BogdanVcode/fotobudka-dashboard/assets/references/04-module.png

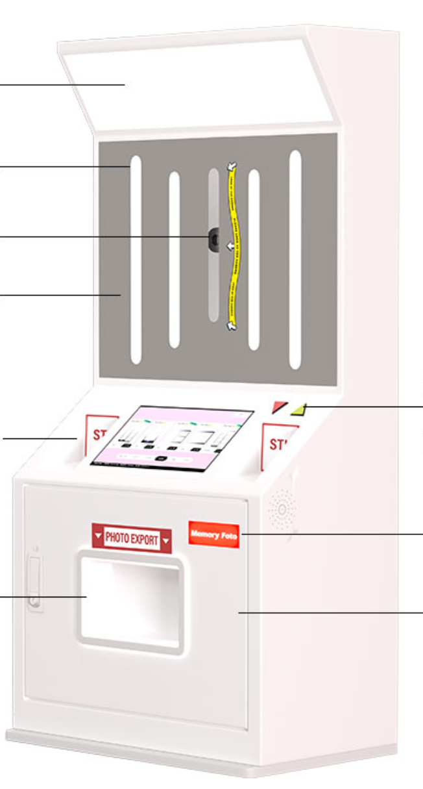
assets/references/04-module.png
