BogdanVcode/fotobudka-dashboard/assets/references/05-profile-correction.png

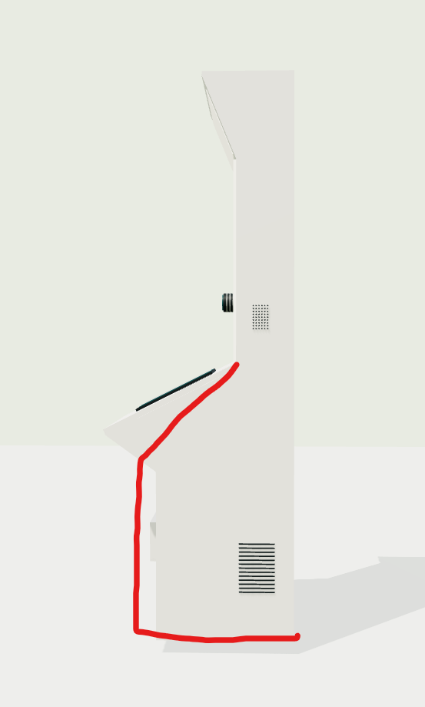
assets/references/05-profile-correction.png
