BogdanVcode/fotobudka-dashboard/render-exterior-07.png

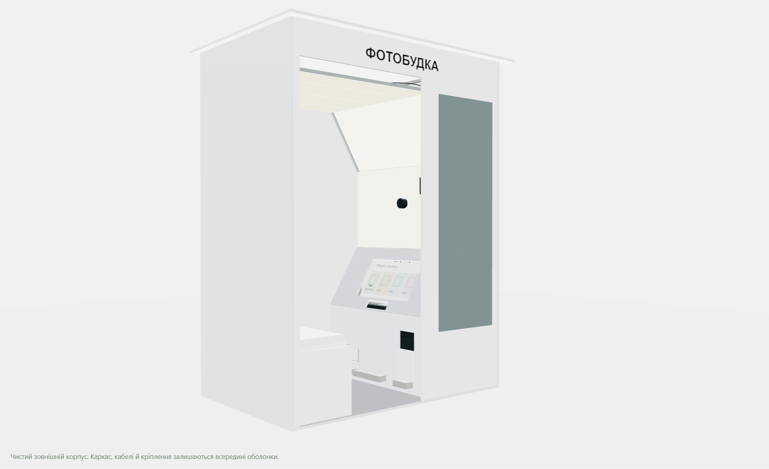
render-exterior-07.png
