BogdanVcode/fotobudka-dashboard/camera-module/wiring-overview.png

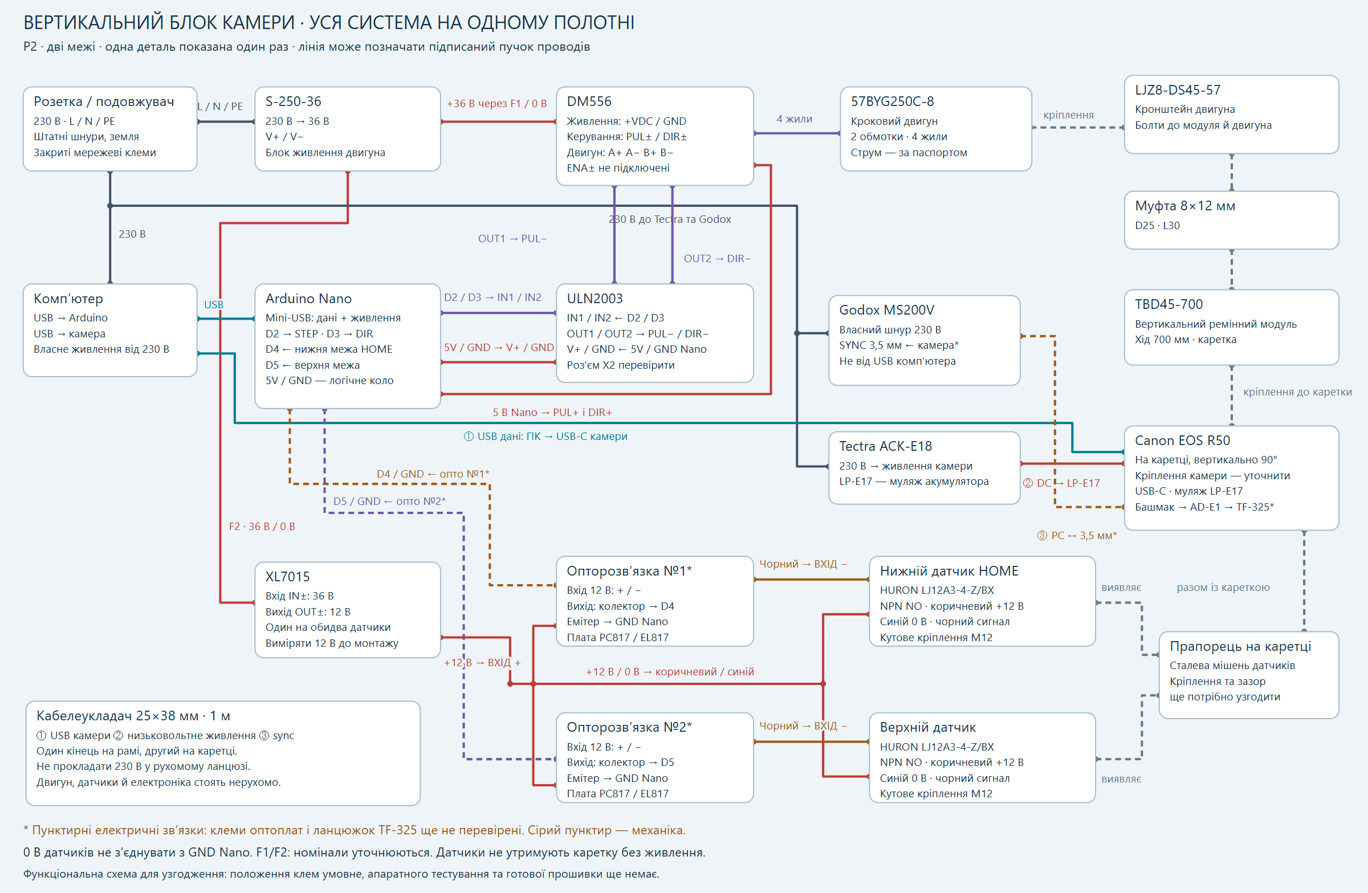
camera-module/wiring-overview.png
